PHochmann/Senso/Hardware/SensoCard/SensoCard-Schematic.png

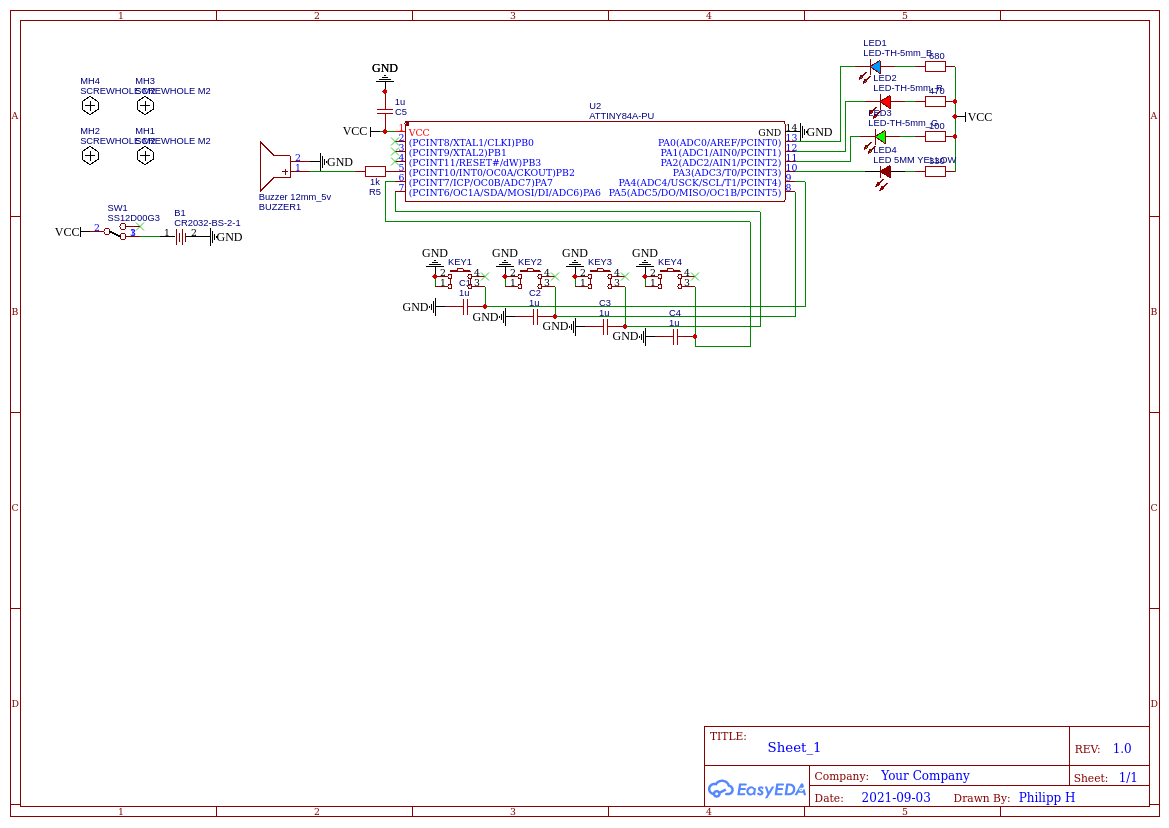
Hardware/SensoCard/SensoCard-Schematic.png
