PHochmann/Senso/Hardware/SensoCard/SensoCard_assembled2.jpg

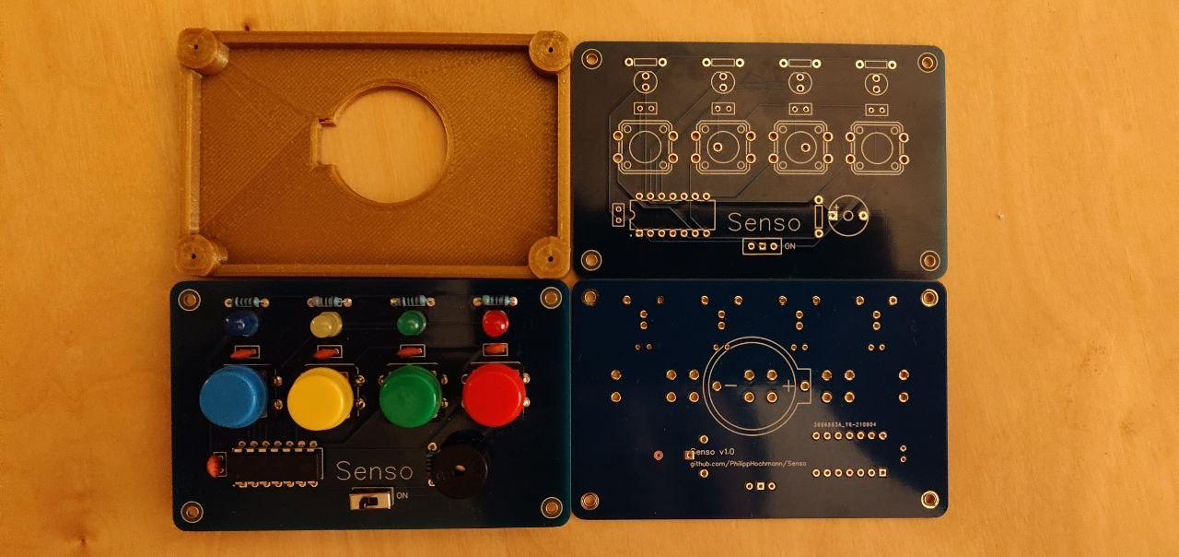
Hardware/SensoCard/SensoCard_assembled2.jpg
