PHochmann/Senso/src/display.h

#include <stdint.h>

// Normal use
void display_init();
void display_show_number(uint8_t number);
void display_clear();

// Used to display something else manually
void display_send(uint8_t bits);
void display_show();
